justharryjust/AVCTeam3/Hardware/upperrobot.jpg

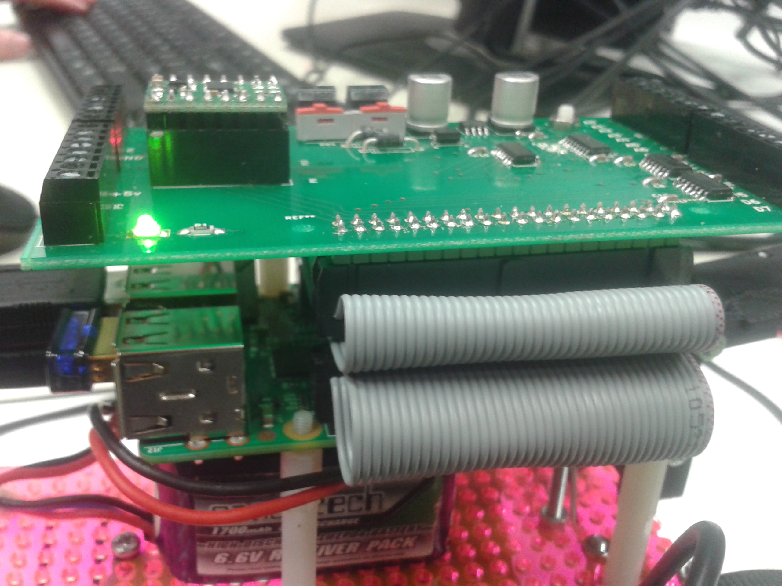
Hardware/upperrobot.jpg
