justharryjust/AVCTeam3/Hardware/wheel1.jpg

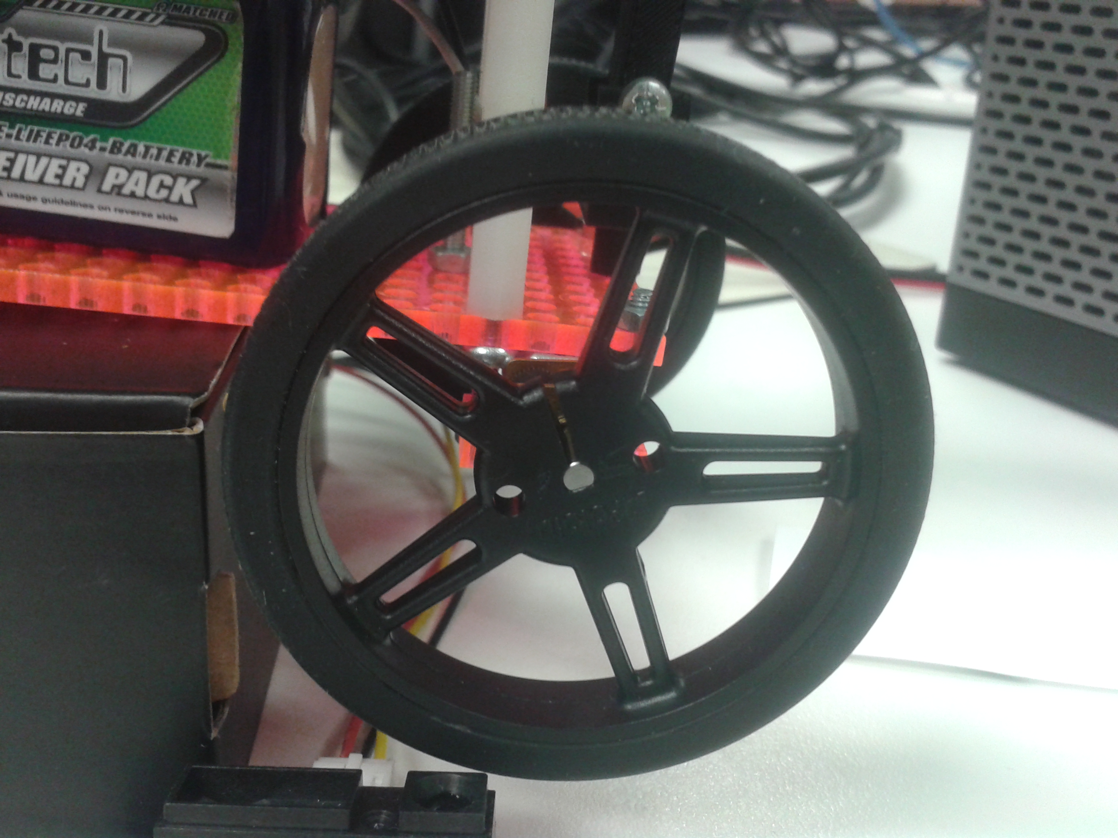
Hardware/wheel1.jpg
