justharryjust/AVCTeam3/Pictures/frontRobot.jpg

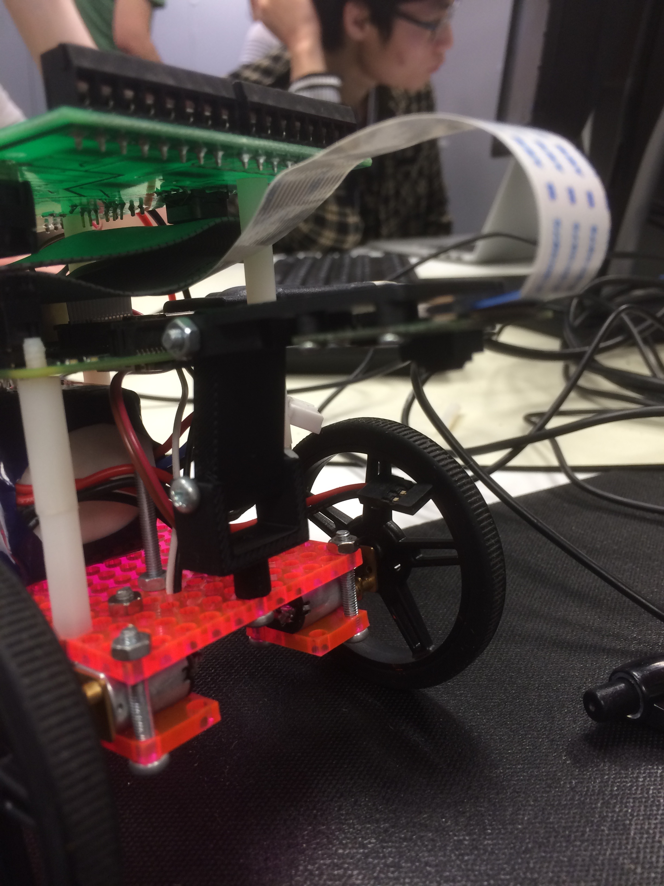
Pictures/frontRobot.jpg
