justharryjust/AVCTeam3/Pictures/mazePic 1.jpg

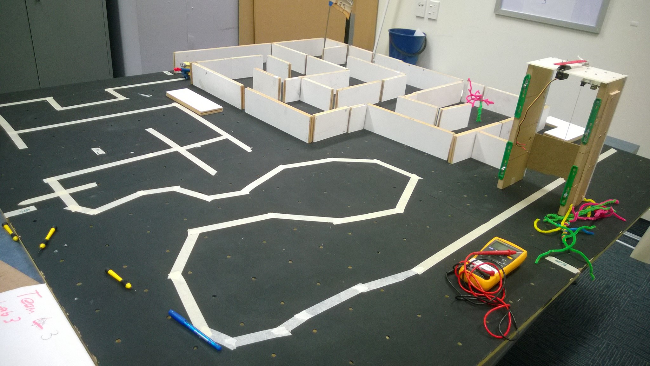
Pictures/mazePic 1.jpg
