justharryjust/AVCTeam3/Pictures/MazePic 2.jpg

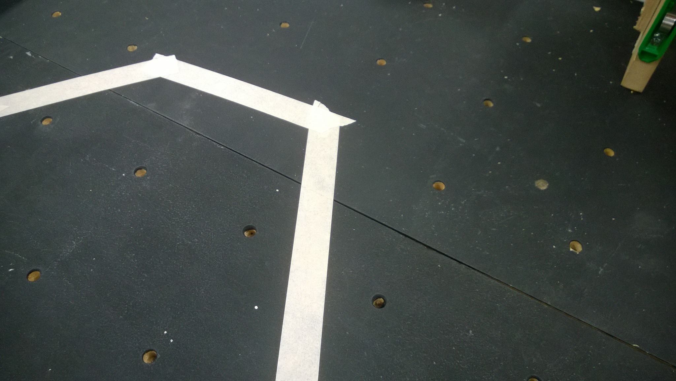
Pictures/MazePic 2.jpg
