justharryjust/AVCTeam3/Pictures/Team Agreement.jpg

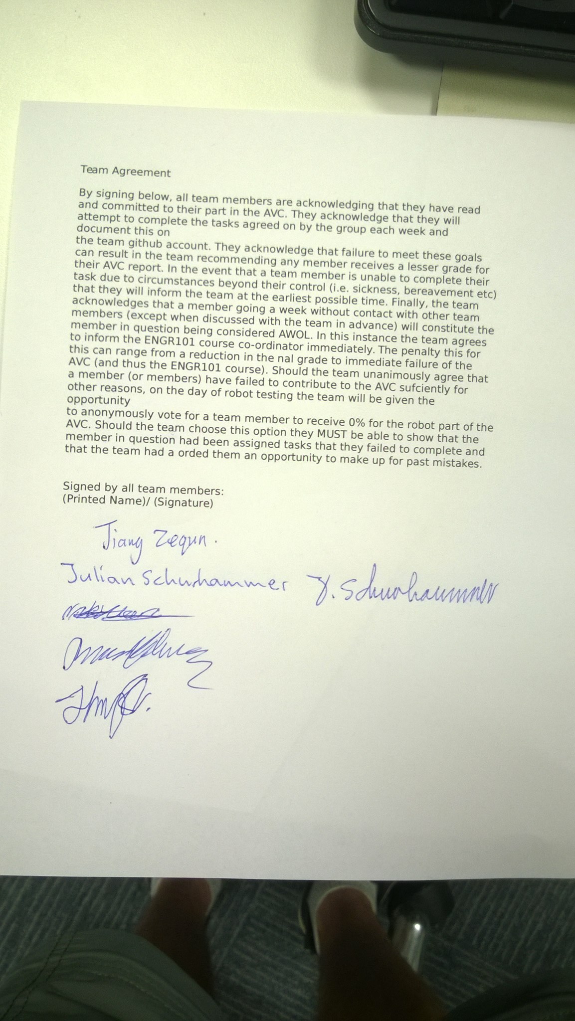
Pictures/Team Agreement.jpg
