justharryjust/AVCTeam3/Pictures/tempWheel2.jpg

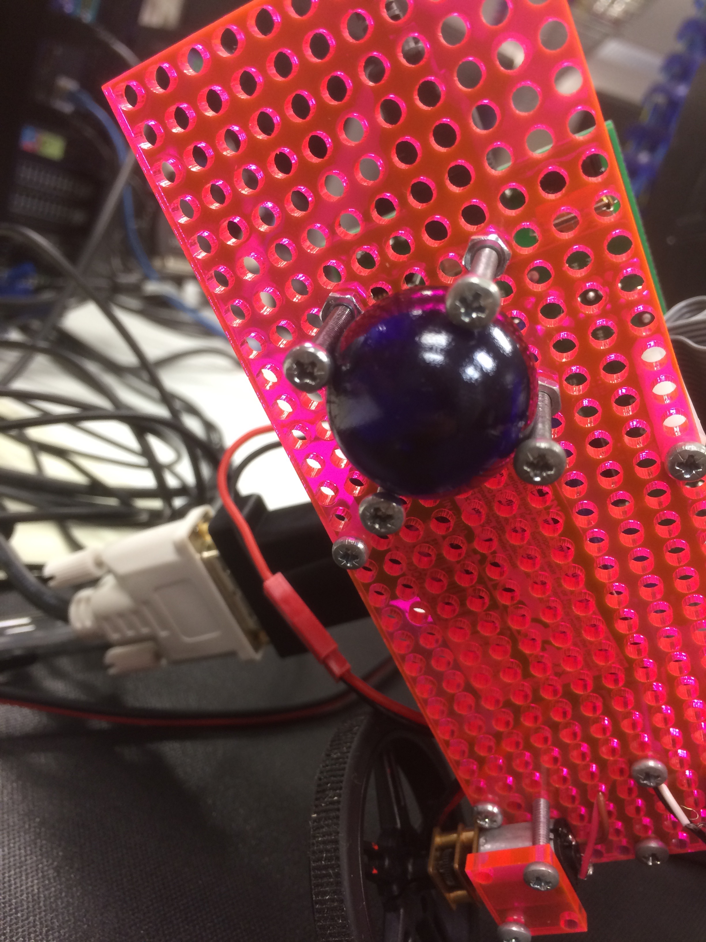
Pictures/tempWheel2.jpg
