justharryjust/AVCTeam3/Pictures/tempWheel.jpg

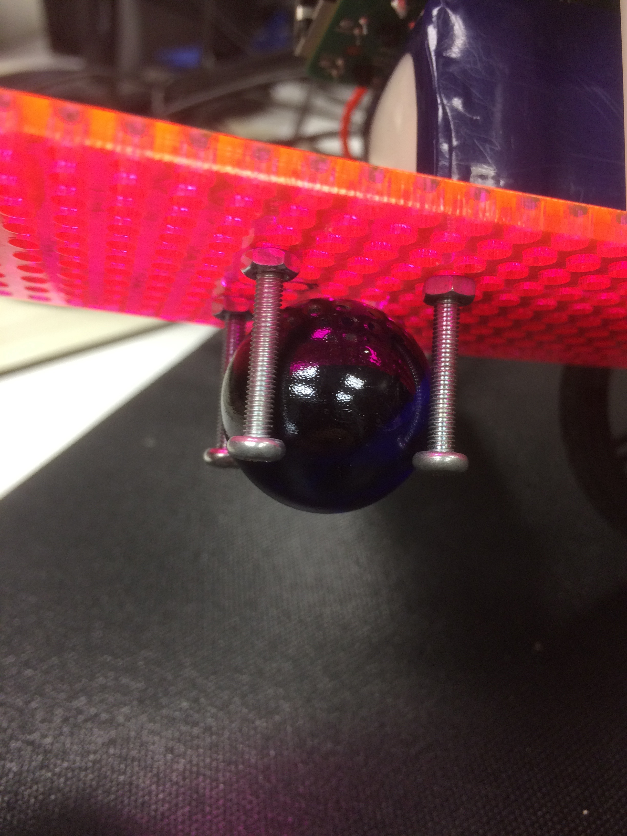
Pictures/tempWheel.jpg
