justharryjust/AVCTeam3/Code/main2.cpp

#include <iostream>
#include <stdio.h>
#include <time.h>

extern "C" int init(int d_level);
extern "C" int Sleep(int sec, int usec);
extern "C" int set_motor(int motor, int value);
extern "C" int take_picture();
extern "C" int get_pixel(int row, int col, int colour);
extern "C" int open_screen_stream();
extern "C" int close_screen_stream();
extern "C" int update_screen();

using namespace std;

const int white_value = 110;
const int camera_y_coord = 160;
const int min_line_width = 10;
const float speed = 0.8;
//Set PID in different error methods
float P = 0;
float I = 0;
float D = 0;
float max_error = 0;

//Restrict val between a and b
int clamp(int a, int b, int val){
    if(val < a){
        return a;
    }
    if(val > b){
        return b;
    }
    return val;
}

int error_method_1(){
    //PID Constants for method 1
    P = 0.05;
    I = 0.001;
    D = 0.0;
    max_error = 10000;

    int error = 0;
    for (int i = 0;i<320;i++) {
        int value = get_pixel(i, camera_y_coord, 3);
        if (value>white_value) {
            error += i-160;
        }
    }
    return error;
}

int error_method_2(){
    //PID Constants for method 2
    P = 0.5;
    I = 0.0;
    D = 0.0;
    max_error = 160;

    int left = 0;
    for (int i = 0;i<160;i++) {
        int value = get_pixel(i, camera_y_coord, 3);
        if (value>white_value) {
            left = 160 - i;
        }
    }
    int right = 0;
    for (int i = 320;i>=160;i--) {
        int value = get_pixel(i, camera_y_coord, 3);
        if (value>white_value) {
            right = i-160;
        }
    }
    return right - left;
}

int error_method_3(){
    //PID Constants for method 3
    P = 0.8;
    I = 0.0;
    D = 0.0;
    max_error = 160;

    int left = 0;
    int consec_white_pixels = 0;
    for (int i = 0;i<160;i++) {
        int value = get_pixel(i, camera_y_coord, 3);
        if (value>white_value) {
			consec_white_pixels += 1;
			if(consec_white_pixels >= min_line_width){
				left = 160 - (i - consec_white_pixels);
			}
        } else {
			consec_white_pixels = 0;
		}
    }
    int right = 0;
    consec_white_pixels = 0;
    for (int i = 320;i>=160;i--) {
        int value = get_pixel(i, camera_y_coord, 3);
        if (value>white_value) {
			consec_white_pixels += 1;
			if(consec_white_pixels >= min_line_width){
				right = i + consec_white_pixels - 160;
			}
        } else {
			consec_white_pixels = 0;
		}
    }
    return right - left;
}

bool has_lost_line(){
	int consec_white_pixels = 0;
    for (int i = 0;i<320;i++) {
        int value = get_pixel(i, camera_y_coord, 3);
        if (value>white_value) {
			consec_white_pixels += 1;
            if(consec_white_pixels >= min_line_width){
				return false;
			}
        } else {
			consec_white_pixels = 0;
		}
    }
    return true;
}

int main()
{
    init(0);
    open_screen_stream();

    int integral = 0;
    int last_error = error_method_1();

    while (true) {
            take_picture();
            update_screen();

            //Remember to change last_error when changing the method
            int error = error_method_3();
            if(has_lost_line()){
                if(last_error > 0){
                    error = max_error;
                } else if(last_error < 0){
                    error = 0 - max_error;
                }
            }
            integral += error;
            int derivitive = last_error - error;
            last_error = error;
            int final_signal = P*error + I*integral + D*derivitive;

            cout << "error " << error << endl;
            cout << "integral " << integral << endl;
            cout << "derivitive " << derivitive << endl;
            cout << "final " << final_signal << endl;

            set_motor(1 , speed*clamp(0, 100, 100+final_signal));
            set_motor(2 , speed*clamp(0, 100, 100-final_signal));
    }
    return 0;
}
